Makerfabs/ESP32-S3-Parallel-TFT-with-Touch-1.9inch/example/scoreboard/scoreboard.ino

#include <lvgl.h>
#include "ui.h"
#include <Arduino_GFX_Library.h>

#define TOUCH_MODULES_CST_SELF
#include <TouchLib.h>

#include "pin_config.h"

static const uint16_t screenWidth = 320;
static const uint16_t screenHeight = 170;

static lv_disp_draw_buf_t draw_buf;
static lv_color_t buf[screenWidth * screenHeight / 10];

Arduino_DataBus *bus = new Arduino_ESP32LCD8(47 /* DC */, 46 /* CS */, 38 /* WR */, 39 /* RD */, 9 /* D0 */, 10 /* D1 */, 11 /* D2 */, 12 /* D3 */,
                                             13 /* D4 */, 14 /* D5 */, 15 /* D6 */, 16 /* D7 */);

Arduino_GFX *gfx = new Arduino_ST7789(bus, 48 /* RST */, 0 /* rotation */, true /* IPS */, 170 /* width */, 320 /* height */, 35 /* col offset 1 */,
                                      0 /* row offset 1 */, 35 /* col offset 2 */, 0 /* row offset 2 */);

TouchLib touch(Wire, PIN_IIC_SDA, PIN_IIC_SCL, CTS820_SLAVE_ADDRESS, PIN_TOUCH_RES);

int left_num = 0;
int right_num = 0;

void setup()
{
    USBSerial.begin(115200); /* prepare for possible serial debug */

    pinMode(PIN_LCD_BL, OUTPUT);
    digitalWrite(PIN_LCD_BL, HIGH);

    pinMode(PIN_LCD_RST, OUTPUT);
    digitalWrite(PIN_LCD_RST, HIGH);

    pinMode(PIN_TOUCH_RES, OUTPUT);
    digitalWrite(PIN_TOUCH_RES, LOW);
    delay(500);
    digitalWrite(PIN_TOUCH_RES, HIGH);

    ledcSetup(0, 2000, 8);
    ledcAttachPin(PIN_LCD_BL, 0);
    ledcWrite(0, 255);

    Wire.begin(PIN_IIC_SDA, PIN_IIC_SCL);
    touch.init();

    SPI.begin(SD_SCK, SD_MISO, SD_MOSI);
    gfx->begin();
    gfx->setRotation(1);

    String LVGL_Arduino = "Hello Arduino! ";
    LVGL_Arduino += String('V') + lv_version_major() + "." + lv_version_minor() + "." + lv_version_patch();

    USBSerial.println(LVGL_Arduino);
    USBSerial.println("I am LVGL_Arduino");

    lv_init();
    lv_disp_draw_buf_init(&draw_buf, buf, NULL, screenWidth * screenHeight / 10);

    /*Initialize the display*/
    static lv_disp_drv_t disp_drv;
    lv_disp_drv_init(&disp_drv);
    /*Change the following line to your display resolution*/
    disp_drv.hor_res = screenWidth;
    disp_drv.ver_res = screenHeight;
    disp_drv.flush_cb = my_disp_flush;
    disp_drv.draw_buf = &draw_buf;
    lv_disp_drv_register(&disp_drv);

    /*Initialize the (dummy) input device driver*/
    static lv_indev_drv_t indev_drv;
    lv_indev_drv_init(&indev_drv);
    indev_drv.type = LV_INDEV_TYPE_POINTER;
    indev_drv.read_cb = my_touchpad_read;
    lv_indev_drv_register(&indev_drv);

    ui_init();

    USBSerial.println("Setup done");
}

void loop()
{
    lv_timer_handler(); /* let the GUI do its work */
    delay(5);
}

//------------------------------------------------------------------------

/* Display flushing */
void my_disp_flush(lv_disp_drv_t *disp, const lv_area_t *area, lv_color_t *color_p)
{
    uint32_t w = (area->x2 - area->x1 + 1);
    uint32_t h = (area->y2 - area->y1 + 1);

#if (LV_COLOR_16_SWAP != 0)
    gfx->draw16bitBeRGBBitmap(area->x1, area->y1, (uint16_t *)&color_p->full, w, h);
#else
    gfx->draw16bitRGBBitmap(area->x1, area->y1, (uint16_t *)&color_p->full, w, h);
#endif

    lv_disp_flush_ready(disp);
}

/*Read the touchpad*/
void my_touchpad_read(lv_indev_drv_t *indev_driver, lv_indev_data_t *data)
{
    uint16_t touchX = 0, touchY = 0;

    if (touch.read())
    {
        data->state = LV_INDEV_STATE_PR;

        uint8_t n = touch.getPointNum();
        for (uint8_t i = 0; i < n; i++)
        {
            TP_Point t = touch.getPoint(i);
            int temp_x = t.y;
            int temp_y = map(t.x, 0, 150, 170, 0);

            data->point.x = temp_x;
            data->point.y = temp_y;
            break;
        }
    }
    else
    {
        data->state = LV_INDEV_STATE_REL;
    }
}
